NStevenU/Zimodem-AirLink/image/1.jpg

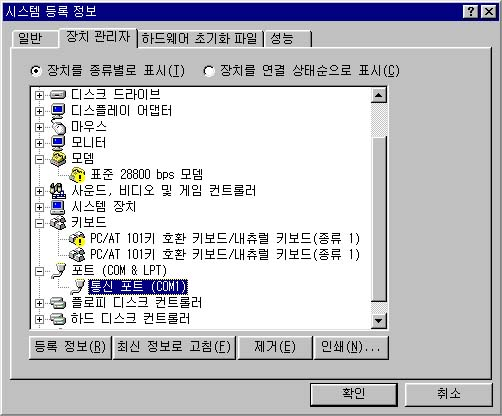
image/1.jpg
