NStevenU/Zimodem-AirLink/image/2.jpg

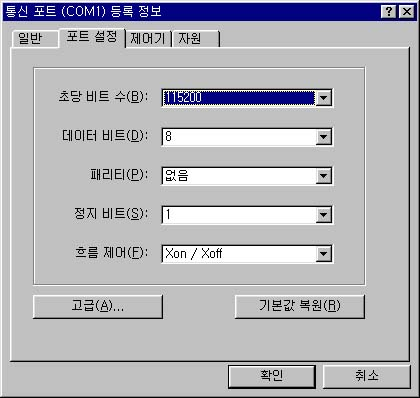
image/2.jpg
